Elektroarzt/simplebus2-mqtt-bridge/hardware/Bridge front.jpeg

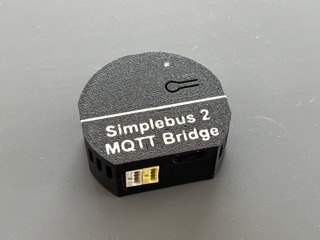
hardware/Bridge front.jpeg
