Elektroarzt/simplebus2-mqtt-bridge/hardware/DIP switch.png

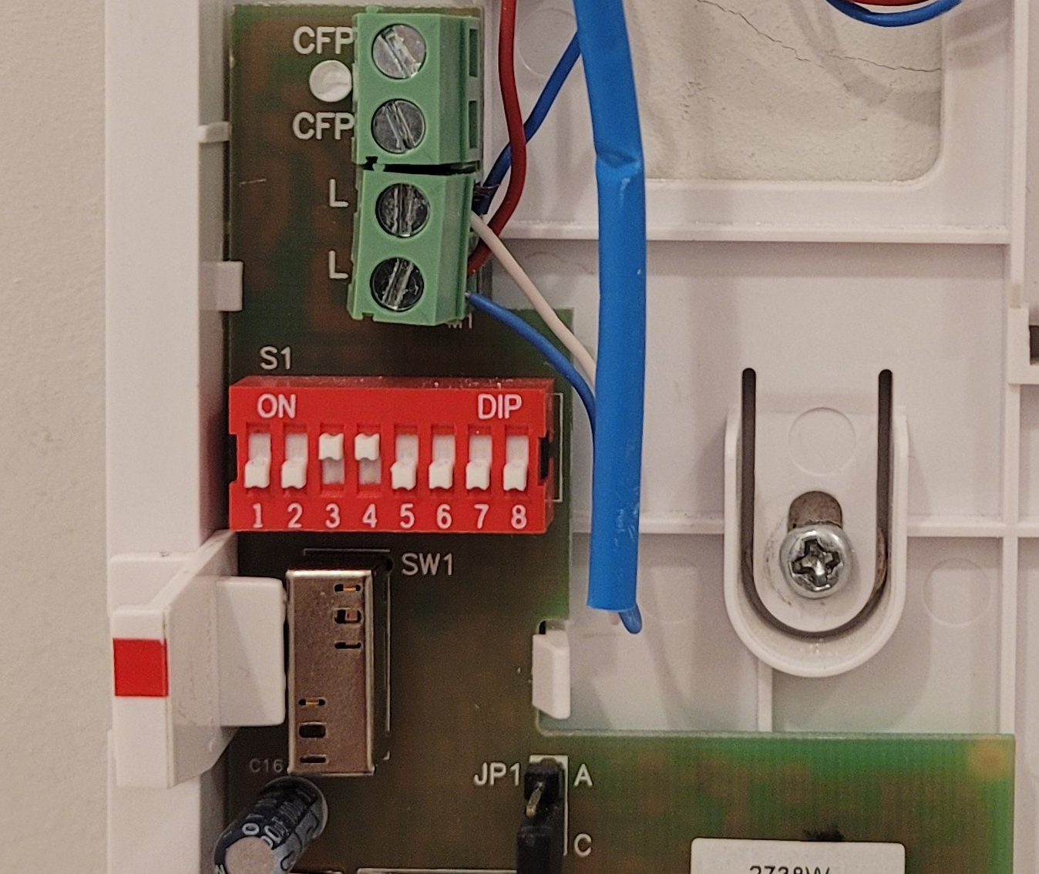
hardware/DIP switch.png
