Elektroarzt/simplebus2-mqtt-bridge/mechanics/Bambu Lab project.png

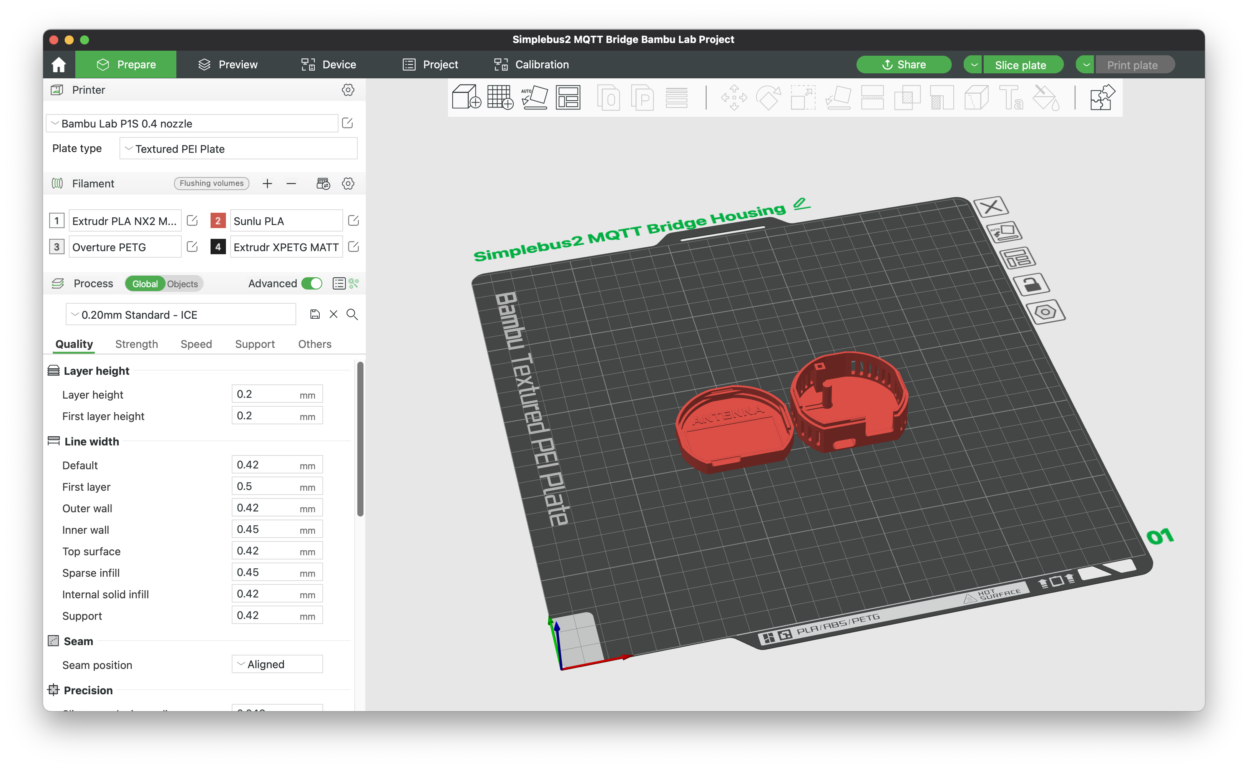
mechanics/Bambu Lab project.png
