Elektroarzt/simplebus2-mqtt-bridge/mechanics/Bottom DIN Rail Mount.png

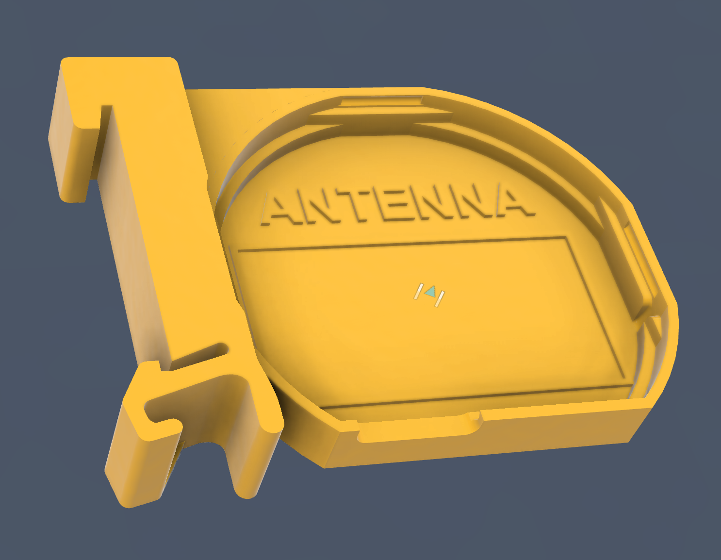
mechanics/Bottom DIN Rail Mount.png
