Elektroarzt/simplebus2-mqtt-bridge/software/WiFi manager/WiFi manager configuration.png

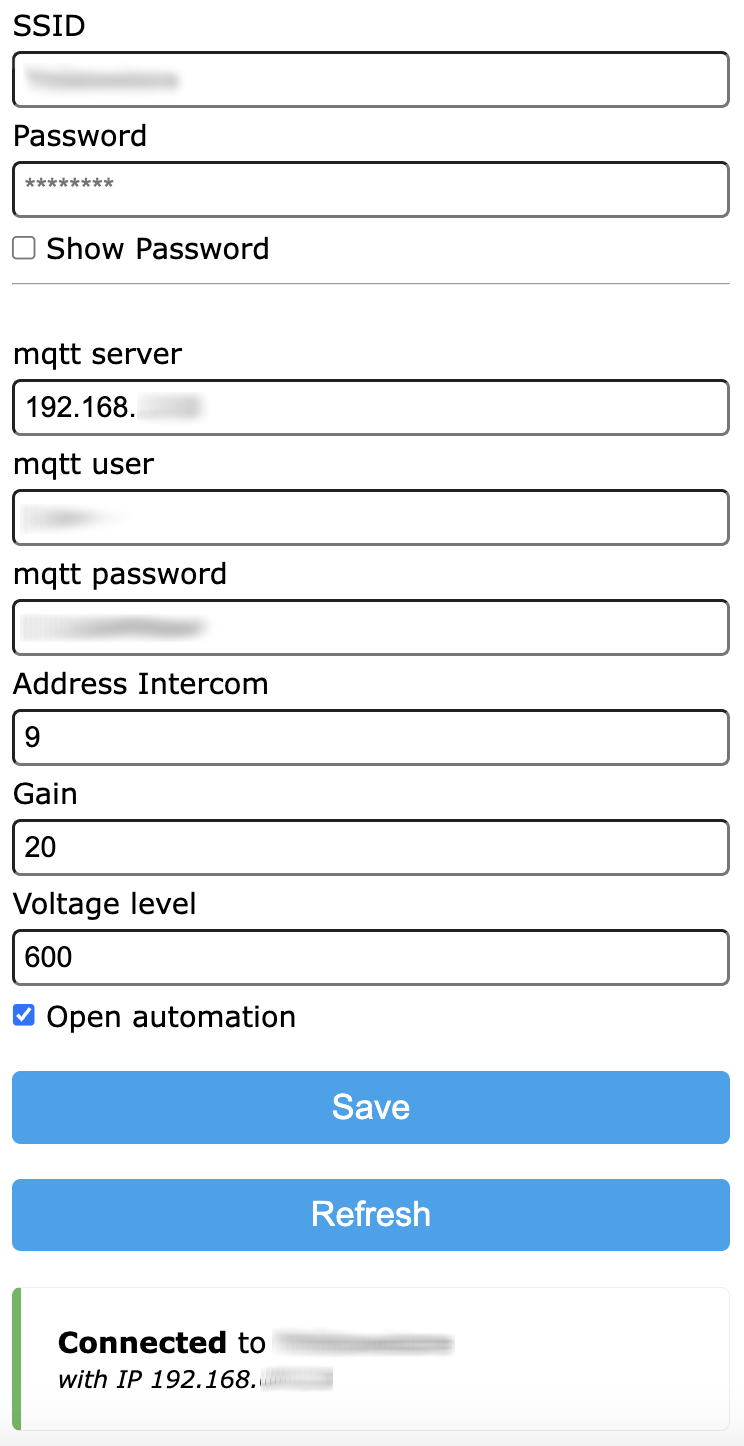
software/WiFi manager/WiFi manager configuration.png
