Elektroarzt/simplebus2-mqtt-bridge/software/WiFi manager/WiFi manager main menu.png

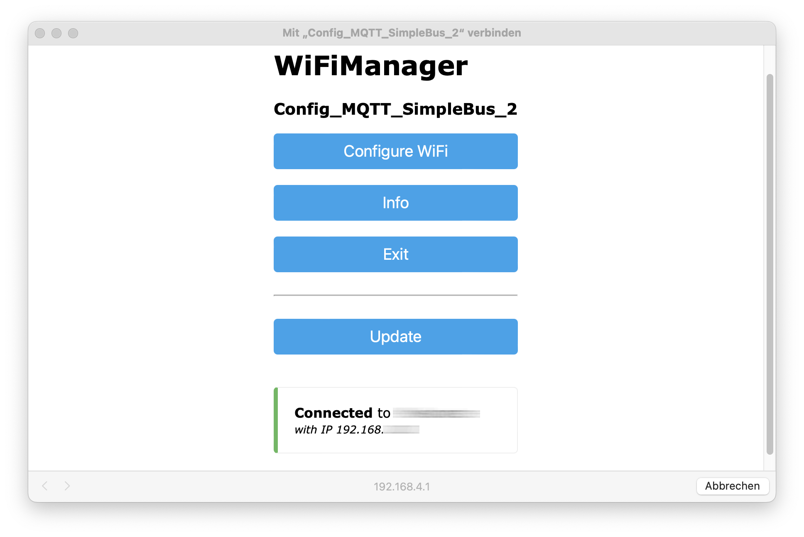
software/WiFi manager/WiFi manager main menu.png
