Elektroarzt/simplebus2-mqtt-bridge/software/WiFi manager/WiFi manager OTA update.png

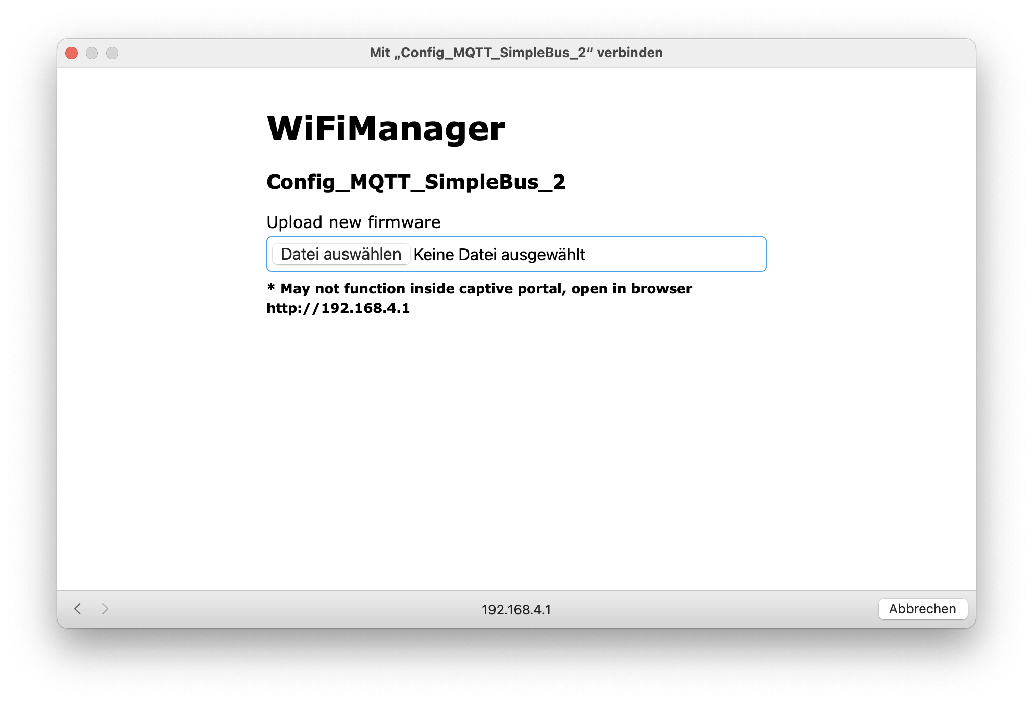
software/WiFi manager/WiFi manager OTA update.png
